yann-cesbron/poseidon/ESPgateway/esp32LilygoLora.jpg

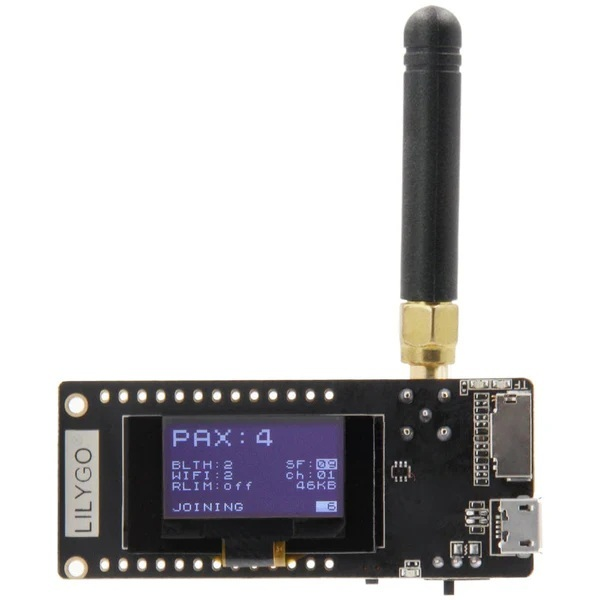
ESPgateway/esp32LilygoLora.jpg
