yann-cesbron/poseidon/ESPsensors/EspS3TrackerStructure.png

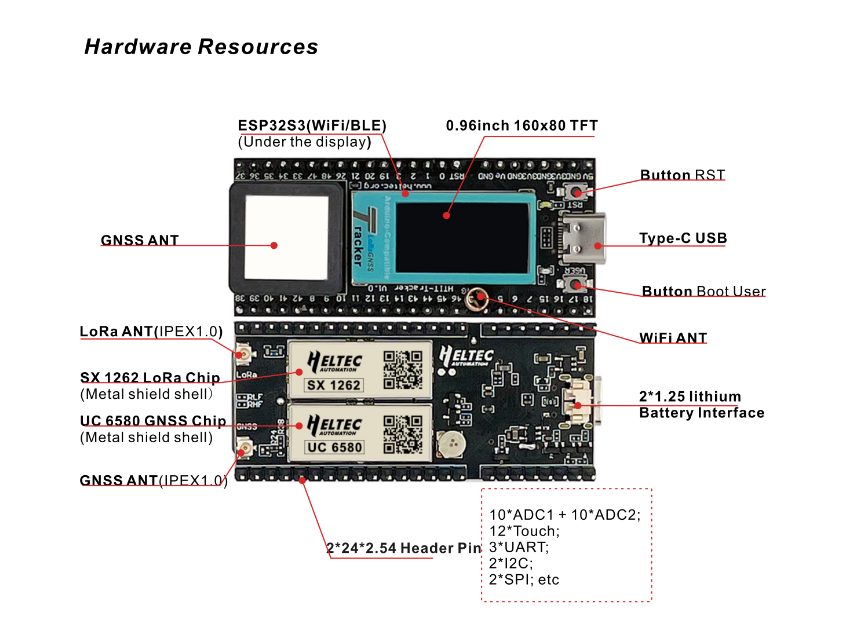
ESPsensors/EspS3TrackerStructure.png
