yann-cesbron/poseidon/Kicad/Detection.kicad_sch

## KiCad design Kicad/Detection.kicad_sch (2025-11-03)

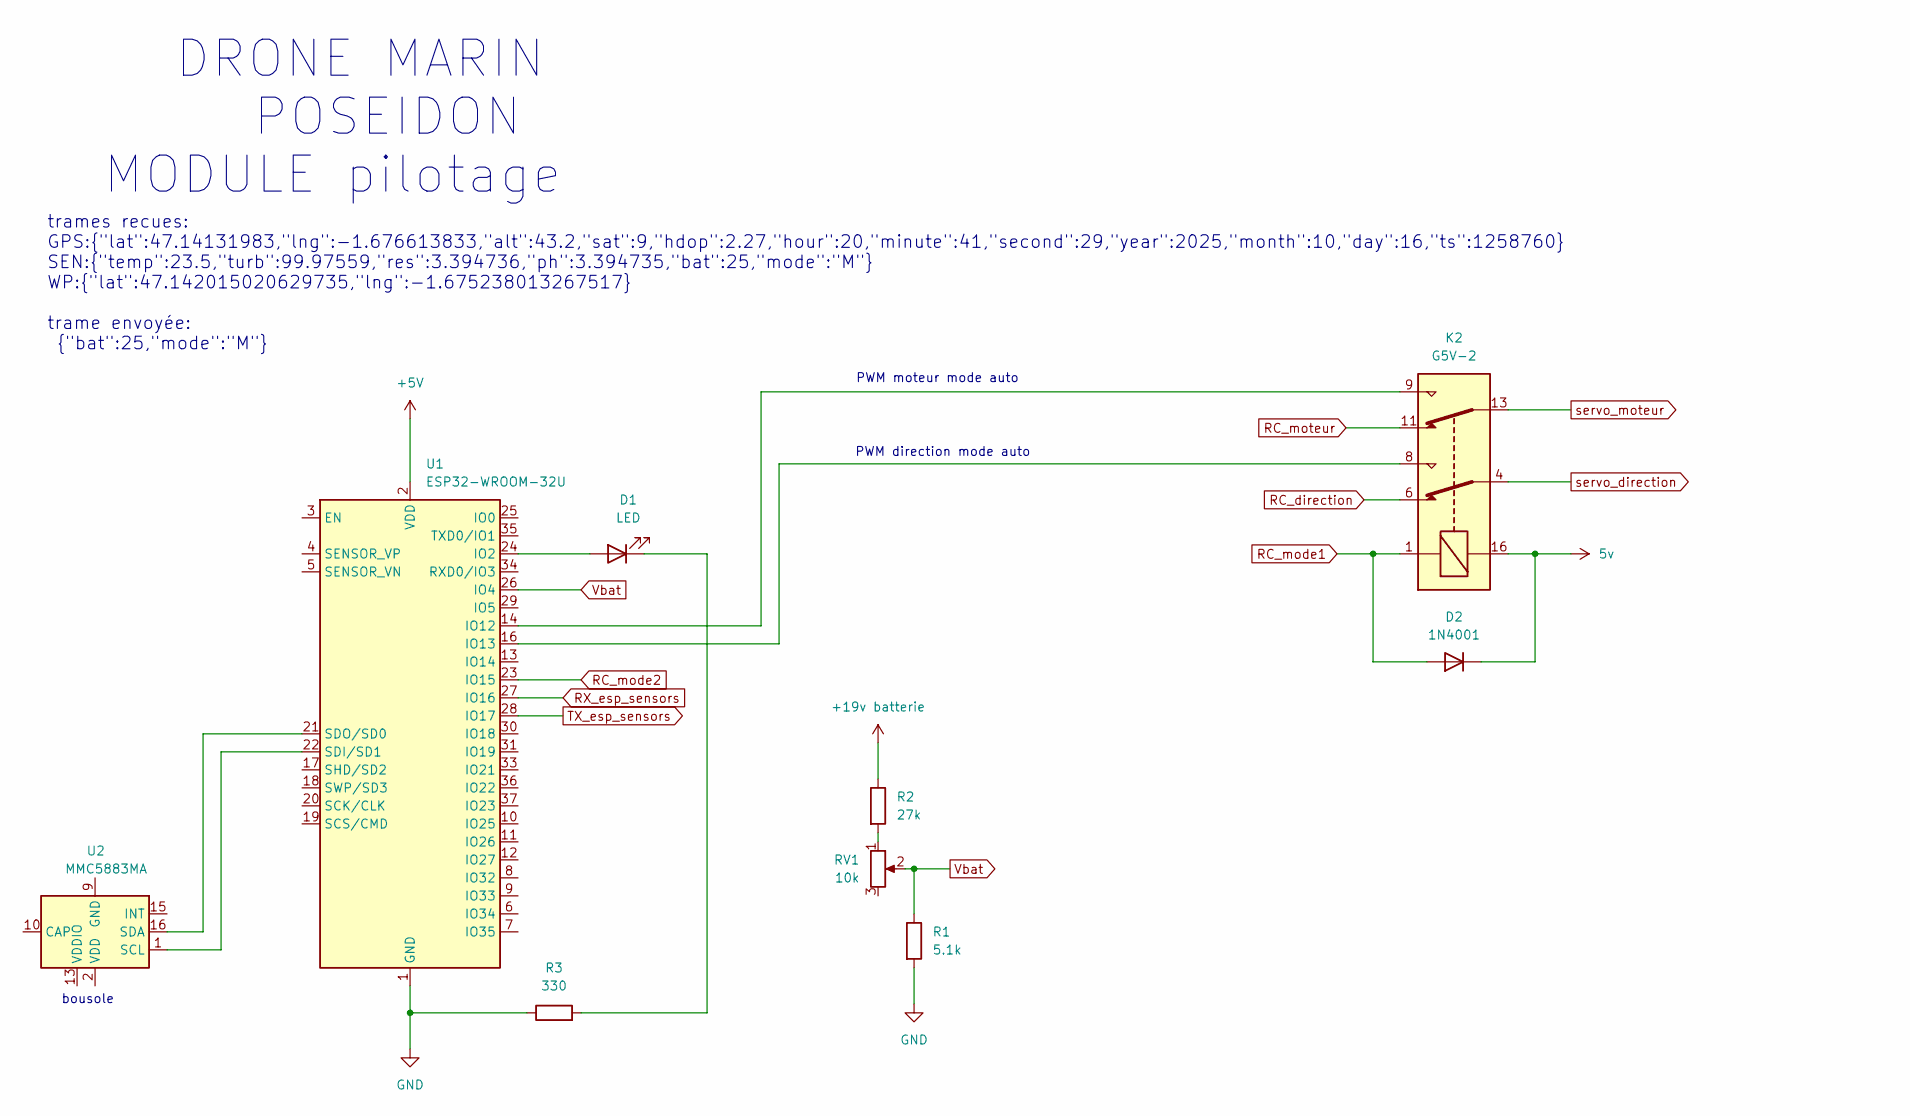
[picture p10: schematic Detection.kicad_sch]

Parts:
D1: LED
D2: 1N4001; D_DO-41_SOD81_P10.16mm_Horizontal
K2: G5V-2; Relay_DPDT_Omron_G5V-2
R1: 5.1k
R2: 27k
R3: 330
RV1: 10k
U1: ESP32-WROOM-32U
U2: MMC5883MA; LGA-16_3x3mm_P0.5mm

Connections:
5v: D2.1 (K), K2.16
+5V: U1.2 (VDD)
+19v batterie: R2.1
GND: R1.2, R3.1, U1.1 (GND), U1.15 (GND), U1.38 (GND), U1.39 (GND)
unnamed: D1.1 (K), R3.2
unnamed: D1.2 (A), U1.24 (IO2)
unnamed: K2.8, U1.16 (IO13)
unnamed: K2.9, U1.14 (IO12)
unnamed: R2.2, RV1.1
unnamed: U1.21 (SDO/SD0), U2.16 (SDA)
unnamed: U1.22 (SDI/SD1), U2.1 (SCL)
unnamed: U2.9 (GND), U2.11 (GND)
RC_direction: K2.6
RC_mode1: D2.2 (A), K2.1
RC_mode2: U1.23 (IO15)
RC_moteur: K2.11
RX_esp_sensors: U1.27 (IO16)
TX_esp_sensors: U1.28 (IO17)
Vbat: R1.1, RV1.2, U1.26 (IO4)
servo_direction: K2.4
servo_moteur: K2.13

Notes on the sheet:
trames recues: GPS:{"lat":47.14131983,"lng":-1.676613833,"alt":43.2,"sat":9,"hdop":2.27,"hour":20,"minute":41,"second":29,"year":2025,"month":10,"day":16,"ts":1258760} SEN:{"temp":23.5,"turb":99.97559,"res":3.394736,"ph":3.394735,"bat":25,"mode":"M"} WP:{"lat":47.142015020629735,"lng":-1.6752380132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
DRONE MARIN POSEIDON MODULE pilotage
PWM direction mode auto
PWM moteur mode auto
bousole
